raszpl/M8SBC-486/photos/IMG_20251005.jpeg

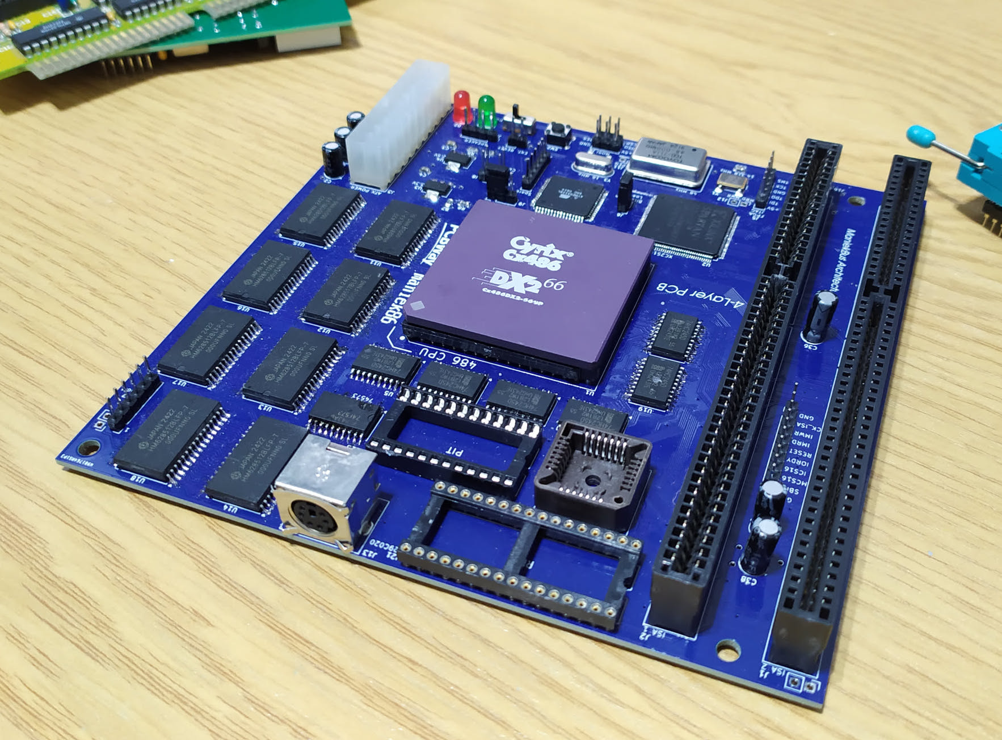
photos/IMG_20251005.jpeg
