raszpl/M8SBC-486/bios/c_src/ide.h

#ifndef IDE_H
#define IDE_H

#include <stdint.h>
#include "x86io.h"
#include "utils.h"
#include "vga.h"
#include "interrupts.h"

#define IDE_DATA 0x1F0
#define IDE_SEC_COUNT 0x1F2
#define IDE_NUM0 0x1F3
#define IDE_NUM1 0x1F4
#define IDE_NUM2 0x1F5
#define IDE_NUM3 0x1F6
#define IDE_COMMAND 0x1F7
#define IDE_STATUS 0x1F7

#define IDE_DEV_CONTROL 0x3F6

void IDE_reset();
int IDE_wait_busy(int timeout);
int IDE_detect(char *drive_name);

#endif
