raszpl/M8SBC-486/bios/c_src/setup.h

#ifndef SETUP_H
#define SETUP_H

#include <stdint.h>
#include "x86io.h"
#include "utils.h"
#include "cpudetect.h"
#include "vga.h"
#include "interrupts.h"
#include "ide.h"
#include "cmos.h"
#include "about.h"

void setup_display(uint16_t cpuid, int is_cyrix, int mem_total, int fpu_present, char *ide_name,  int ide_detected);

#endif
